RASuniandes/SeguidorDeLinea/PCB/librerias/librerias/usini_kicad_sensors-main/usini_kicad_sensors-main/sources/fusion360/audio_3.5mm_trrs.png

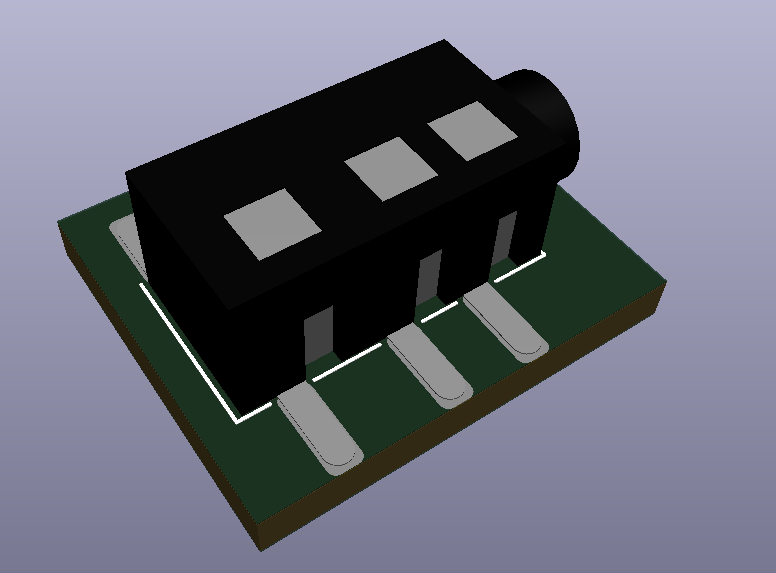
PCB/librerias/librerias/usini_kicad_sensors-main/usini_kicad_sensors-main/sources/fusion360/audio_3.5mm_trrs.png
