RASuniandes/SeguidorDeLinea/PCB/librerias/librerias/usini_kicad_sensors-main/usini_kicad_sensors-main/sources/fusion360/bmp180.png

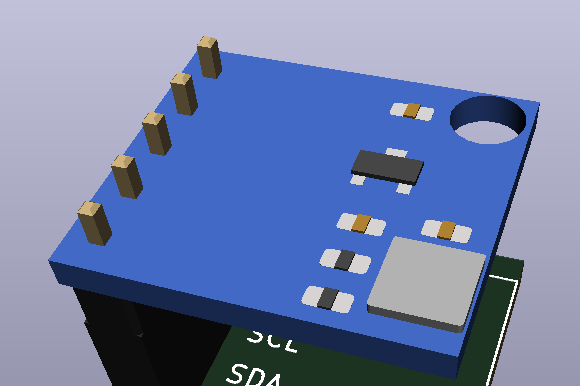
PCB/librerias/librerias/usini_kicad_sensors-main/usini_kicad_sensors-main/sources/fusion360/bmp180.png
