RASuniandes/SeguidorDeLinea/PCB/librerias/librerias/usini_kicad_sensors-main/usini_kicad_sensors-main/sources/fusion360/mpl3115a2.png

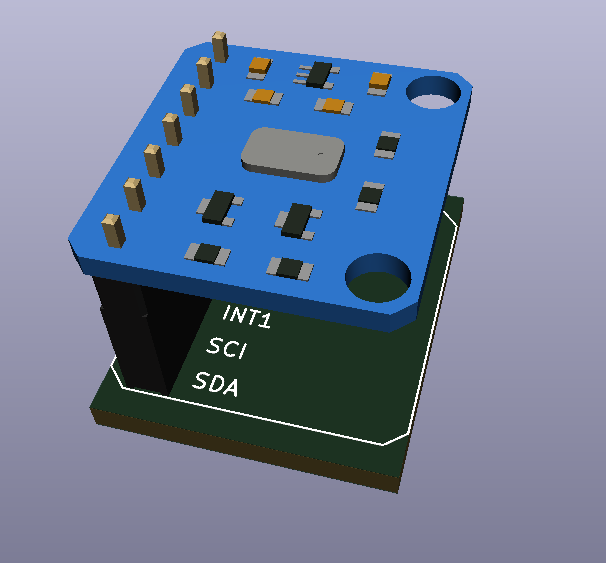
PCB/librerias/librerias/usini_kicad_sensors-main/usini_kicad_sensors-main/sources/fusion360/mpl3115a2.png
